breakeryu/PICO-MAGIX/2.software/Doucument/1.环境配置/图片/image-20220318193846450.png

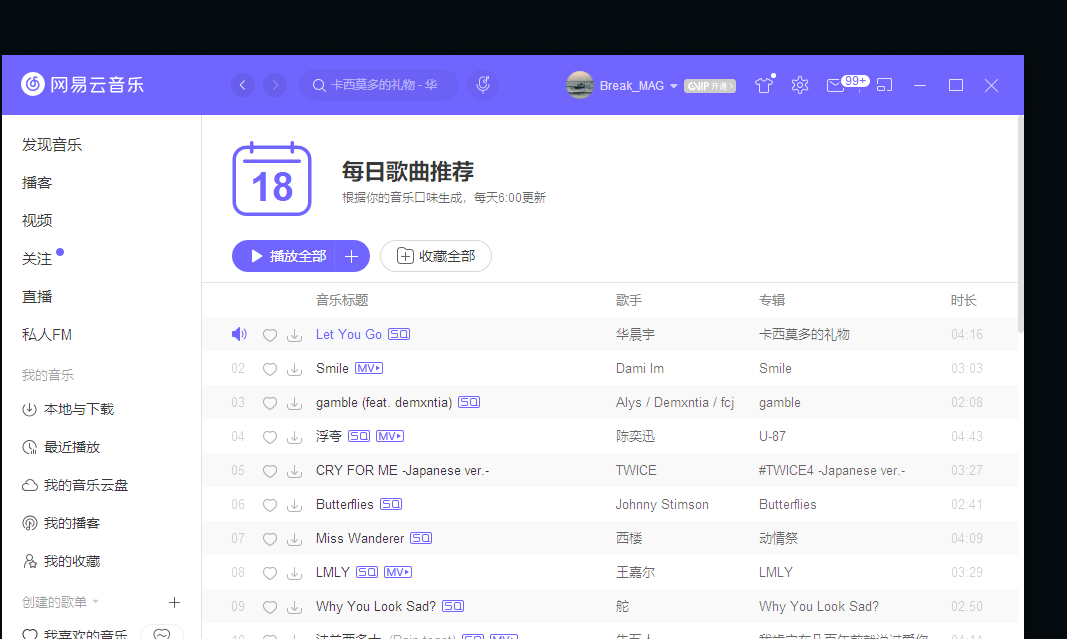
2.software/Doucument/1.环境配置/图片/image-20220318193846450.png
