breakeryu/PICO-MAGIX/2.software/Doucument/上位机/测控大师工程/控制台demo/图标/图标-传感器读取.png

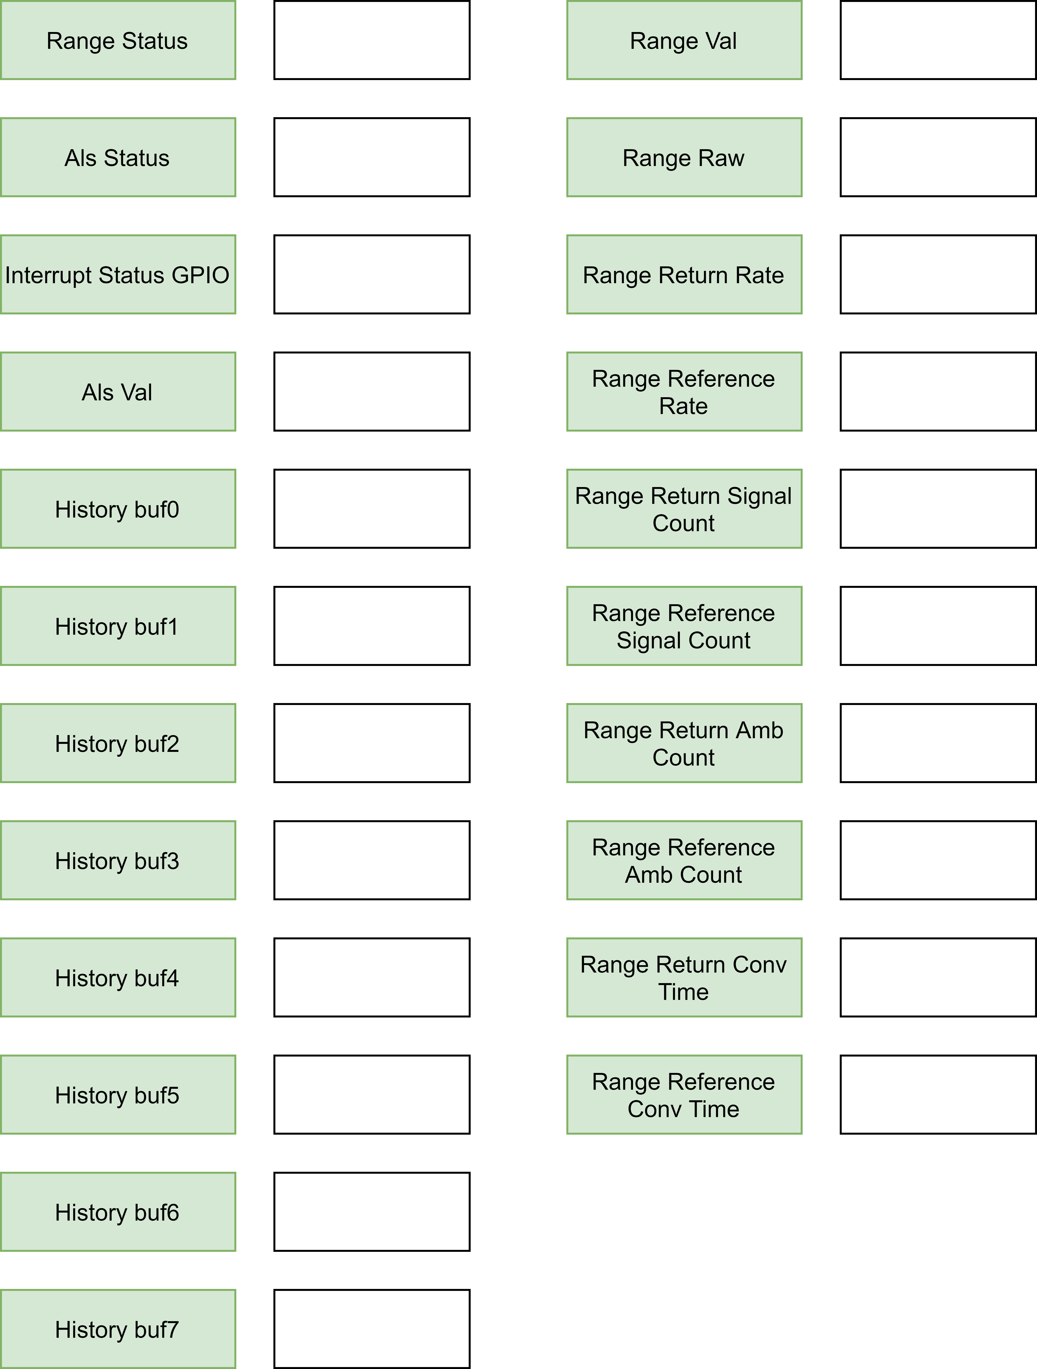
2.software/Doucument/上位机/测控大师工程/控制台demo/图标/图标-传感器读取.png
